aschmidt99/LTDM_Kit_RevC/Electronics/spice_simulations/Draft1.asc

R1: res; {R}
R2: res; {R}
R3: res; {R}
R4: res; {R}
U1: UniversalOpAmp2; Avol=100K GBW=300Meg Slew=140Meg
V1: voltage; PULSE(0 3.3 0 5n 5n 15u 50u 10)
V2: voltage; 12
V3: voltage; 12
Named nets: 0, -12V, +12V
.tran .00002
.step param R list 100 1k 10k
