aschmidt99/LTDM_Kit_RevC/Electronics/spice_simulations/Input_Stage.asc

A1: sample
B1: bv; V=V(act) + V(vib) + V(actback)
C1: cap; 60p
C2: cap; 60p
C3: cap; 0
R1: res; 2.2
R2: res; 0
R3: res; 1k
R4: res; 100
R5: res; 100
R6: res; 1k
R7: res; 3.1k
R8: res; .5
R9: res; 31k
R10: res; 100
R11: res; 1.47k
R12: res; 100
R13: res; 1k
R14: res; 1k
R15: res; 100
R16: res; 1.47k
R17: res; 100
R18: res; 1k
U1: UniversalOpAmp2
U2: UniversalOpAmp2
U3: UniversalOpAmp2
U4: UniversalOpAmp2
V1: voltage; SINE(0 1m 1000 0 0 0 50)
V2: voltage; 12
V3: voltage; 12
V4: voltage; SINE(0 10m 500 0 0 0 50)
V5: voltage; SINE(0 -1m 1000 0 0 0 50)
V6: voltage; SINE(0 0 100 0 0 0 50)
V7: voltage; PULSE(0 12 10u 1n 1n 25u 50u 1000)
V8: voltage; PULSE(0 5 2u 1n 1n 15u 50u 1000)
V9: voltage; PULSE(0 -12 35u 1n 1n 2u 50u 1000)
Named nets: 0, +12, -12, act, vib, actback
.tran 0.0001
*.step param R list 470 1k 10k
