aschmidt99/LTDM_Kit_RevC/Electronics/spice_simulations/LF-TIME-MULTIPLEX-ACTUATION+SENSE.asc

10k: res; 1k
11: res; 11
A1: sample
A2: sample
A3: xor
A4: and
A5: and
B1: bv; V= V(vib) + V(STRING_IN)
B2: bv; V= IF(V(ramp) < V(vib), 3.3V, 0)
B3: bv; V= IF(V(ramp) < -V(vib), 3.3V, 0)
B4: bv; V= V(vib)*496
B5: bv; V{if(V(over_current)>100mV, 3.3V, 0)}
B6`: bi; I=1-V(over_current_flag)
C1: cap; 100p
C2: cap; 60p
C3: cap; 60p
C4: cap; 0
C5: cap; 220p
C6: cap; 220p
C7: cap; 220p
C8: cap; 10n
C9: cap; 10n
C10: cap; 20n
C11: cap; 10n
C12: cap; 4.7n
C13: cap; 1000µ
C14: cap; 220µ
C15: cap; 10µ
C16: cap; 100n
D1: TVSdiode
I1: current; 10m
L1: ind; .47µ
L2: ind; .05µ
L3: ind; 0.05µ
M1: pmos; FQB11P06
M2: nmos
M3: nmos; BSC205N10LS
Q1: npn; 2N3904
Q3: pnp; 2N3906
R1: res; 220
R2: res; 470
R3: res; 2
R4: res; 220
R5: res; 100
R6: res; 470
R7: res; 1k
R8: res; .1
R9: res; 100
R10: res; 1k
R11: res; 3.1k
R12: res; 31k
R13: res; 100
R14: res; 1.47k
R15: res; 100
R16: res; .5
R17: res; 1k
R18: res; 1k
R19: res; 100
R20: res; 1.47k
R21: res; 100
R22: res; 11
R23: res; 1k
R24: res; 1k
R25: res; 1k
R26: res; 1k
R27: res; 1k
R28: res; 221
R29: res; 1k
R30: res; 100
R31: res; 0.05
R32: res; 221
R33: res; 1k
R34: res; 100
R35: res; .5
R36: res; 800
R37: res; 800
R38: res; 1k
R39: res; 10k
R40: res; 400
R41: res; 2.2k
R42: res; 2.2k
R43: res; 220
R44: res; 1k
R45: res; 1k
R46: res; 1k
R47: res; 1k
R48: res; 1k
R49: res; 10k
U1: UniversalOpAmp2
U2: UniversalOpAmp2
U3: UniversalOpAmp2
U4: UniversalOpAmp2
U5: UniversalOpAmp2
U6: UniversalOpAmp2
U7: UniversalOpAmp2
U8: UniversalOpAmp2
U9: UniversalOpAmp2
U10: UniversalOpAmp
U11: UniversalOpAmp
U12: UniversalOpAmp
V1: voltage; PULSE(0 5 0 1n 1n 15u 50u 2000)
V2: voltage; 12
V3: voltage; 12
V4: voltage; 3.3
V5: voltage; SINE(0 11m 1k 0 0 0 500); AC 1
V6: voltage; 3.3V
V7: voltage; PULSE(0 1 0 1 0 0 500); AC 1
V8: voltage; PULSE(0 5 2u 1n 1n 15u 50u 1000)
V10: voltage; PULSE(0 12m 10u 30u 0.5n 20u 50u 20000)
Named nets: VEE, 0, VCC, VCC_PRIME, STRING_IN, Current_Sense, vib, ramp, P_PULSE, N_PULSE, SH_preamp_out, preamp_out, SH_out, SUM, SH_preamp_out_2, preamp_out_2, SH_out_2, Pre_SH2, post, S+H, vib_500, LP, TwinT, VCC_prime, 3V3, over_current, over_current_flag
*.tran 0 750u 650u
E = 1 "Left"
B = 2 = "Center"
C = 3 = "RIGHT"
E = 1 "Left"
B = 2 = "Center"
C = 3 = "RIGHT"
G = 1 "Left"
D = 2 "Center"
S = 3 "RIGHT"
G = 1 "Left"
S = 3 "RIGHT"
D = 2 "Center"
Simulation of Lorentz-Force Actuation via time-multiplexing
Found Negative supply solution here: https://forum.allaboutcircuits.com/threads/simplest-way-to-switch-a-negative-voltage-using-logic-level-signals.172313/
Found Positive supply solution here: https://forum.arduino.cc/t/3-3v-logic-to-drive-p-channel-mosfet/685383
RAMP SIGNAL
P_PULSE
P_PULSE
Voltage induced by vibration of string
.tran 2
.lib OPA161x.LIB
Current Limiting Resistor
String Resistance
*.ac dec 1K 10 100K
*.tran 2
XOR to prevent shoot through
