aschmidt99/LTDM_Kit_RevC/Electronics/spice_simulations/LF-TIME-MULTIPLEX-ACTUATION.asc

10k: res; 1k
C1: cap; 100p
D1: schottky; 1N5817
D3: diode
L1: ind; .1µ
L2: ind; .01µ
M1: pmos; FQB11P06
M3: nmos; BSC205N10LS
Q1: npn; 2N3904
Q3: pnp; 2N3906
R1: res; 220
R2: res; 470
R3: res; 1
R4: res; 220
R5: res; 200
R6: res; 470
R7: res; 1k
R8: res; .1
V1: voltage; PULSE(0 3.3 0 .5n 0.5n 15u 100u 20)
V2: voltage; 12
V3: voltage; 12
V4: voltage; PULSE(0 3.3 50u 1n 1n 15u 100u 20)
Named nets: 0, VEE, VCC, STRING_IN, R_sense
.tran 1000u
E = 1 "Left"
B = 2 = "Center"
C = 3 = "RIGHT"
E = 1 "Left"
B = 2 = "Center"
C = 3 = "RIGHT"
G = 1 "Left"
D = 2 "Center"
S = 3 "RIGHT"
G = 1 "Left"
S = 3 "RIGHT"
D = 2 "Center"
Simulation of Lorentz-Force Actuation via time-multiplexing
Found Negative supply solution here: https://forum.allaboutcircuits.com/threads/simplest-way-to-switch-a-negative-voltage-using-logic-level-signals.172313/
Found Positive supply solution here: https://forum.arduino.cc/t/3-3v-logic-to-drive-p-channel-mosfet/685383
