aschmidt99/LTDM_Kit_RevC/Electronics/spice_simulations/Sallen-Key.asc

C2: cap; 10n
C3: cap; 4.7n
R1: res; 2.2k
R2: res; 2.2k
U2: UniversalOpAmp2
V1: voltage; ""; AC 1
V2: voltage; 12
V3: voltage; 12
Named nets: VCC, VEE, 0, in, out
.ac dec 1K 10 20K
