aschmidt99/LTDM_Kit_RevC/Code/LTDM_Kit/LTDM_Kit.ino

/* This code creates precisely timed pulses for sustaining vibrations of a resonant system, like Figure 2 of Paul Vo's Patent: [https://patents.google.com/patent/EP1218716B1](https://patents.google.com/patent/EP1218716B1)

For Teensy 4.1 with RevB or RevC PCB plugged into the UI PCB OR controlled over serial
*/

#include "imxrt.h"
#include "core_pins.h"
#include "debug/printf.h"
#include <Arduino.h>
#include <SPI.h>
#include "SineTable.h"
#include "Adafruit_TLC5947.h"

#include "pinmap.h"
#include "debug.h"
#include "flexpwm.h"
#include "ui.h"
#include "system_config.h"
#include "harmonics.h"
#include "context.h"
#include "render.h"
#include "serialctrl.h"
#include "capture_stream.h"

void setup() {
  delay(2000);               // Wait for 2 seconds before starting the setup
  Serial.begin(2000000);     // Initialize serial communication at 2,000,000 baud rate
  analogReadResolution(12);  // default should be 12
  analogReadAveraging(0);    // Disable averaging (set to 0) for faster reading... 3 seems to be fine, but 4 is far too much
  initUI();                  // initialize the UI (declare pins etc.)
  initFlexPWM();             // initialize FlexPWM
  pinMode(GPIO_PIN, OUTPUT); // set GPIO_PIN as output
  renderSetup(&context);     // setup rendering context
  setInterrupts();           // enable interrupts
  initSineTable();           // initialize sine table
  captureStreamSetup();      // initialize capture stream
}

void loop() {
  captureStreamLoop();       // handle capture stream loop
  pollSerialControl();       // handle serial control polling
  output();                  // update UI and output states
}
