aschmidt99/LTDM_Kit_RevC/Code/LTDM_Kit/debug.h

// debug.h
#ifndef DEBUG_H
#define DEBUG_H

#ifdef DEBUG
  #define DEBUG_PRINT(x)    Serial.print(x)
  #define DEBUG_PRINTLN(x)  Serial.println(x)
#else
  #define DEBUG_PRINT(x)
  #define DEBUG_PRINTLN(x)
#endif

#endif
