aschmidt99/LTDM_Kit_RevC/Code/LTDM_Kit/context.h

// context.h
#ifndef CONTEXT_H
#define CONTEXT_H

#include "system_config.h"
#include "channel.h"

struct LorentzContext {
    // INPUTS - populated by the ISR before render() is called
    Channel ch[2];

    // Hardware inputs
    bool  buttons[16];       // all button states
    float sliders[16];       // all slider/pot values, normalised 0.0-1.0
    float pedals[2];     // both expression pedal values
    uint32_t isrCycleCount;
    uint32_t renderCycleCount;
    unsigned long long frameCount; // total samples elapsed, useful for LFOs etc.
};

extern LorentzContext context;

#endif
