aschmidt99/LTDM_Kit_RevC/Code/LTDM_Kit/ui.cpp

// ui.cpp
#include "ui.h"
#include "pinmap.h"
#include "flexpwm.h"
#include <Arduino.h>
#include <SPI.h>
#include "Adafruit_TLC5947.h"
#include <cstdint>
#include "render.h"
#include "serialctrl.h"
#include "capture_stream.h"

extern float currRMS0;
extern float currRMS1;

volatile bool buttonStates[16] = {};
volatile float sliderStates[16] = {};
volatile float pedalStates[2] = {};

uint8_t currentInput = 0;
bool UI_ReadPhase = false;
uint32_t lastPrint = 0;

float invNumCyclesPerSample = 1.0f;

extern Adafruit_TLC5947 tlc = Adafruit_TLC5947(1, tlc_clock, tlc_data, tlc_latch);

void initUI() {
  pinMode(DSIN, INPUT_PULLUP);
  pinMode(DS0, OUTPUT);
  pinMode(DS1, OUTPUT);
  pinMode(DS2, OUTPUT);
  pinMode(DS3, OUTPUT);

  pinMode(ASIN, INPUT);
  pinMode(AS0, OUTPUT);
  pinMode(AS1, OUTPUT);
  pinMode(AS2, OUTPUT);
  pinMode(AS3, OUTPUT);

  pinMode(FP0, INPUT);
  pinMode(FP1, INPUT);

  digitalWrite(DS0, LOW);
  digitalWrite(DS1, LOW);
  digitalWrite(DS2, LOW);
  digitalWrite(DS3, LOW);
  
  digitalWrite(AS0, LOW);
  digitalWrite(AS1, LOW);
  digitalWrite(AS2, LOW);
  digitalWrite(AS3, LOW);

  tlc.begin();
}

// void initServo(){
//   servo.attach(SERVO_PIN);
// }

// Remap table: reorders where each pot value is stored (since the default hardware inputs was wack)
const uint8_t sliderRemap[16] = {7, 6, 5, 4, 0, 1, 2, 3, 8, 9, 10, 11, 12, 13, 14, 15};

void readUI(){
  if (!UI_ReadPhase) {
    // MUX select pins based on currentButton index
    digitalWrite(DS0, currentInput & 0x01);
    digitalWrite(DS1, (currentInput >> 1) & 0x01);
    digitalWrite(DS2, (currentInput >> 2) & 0x01);
    digitalWrite(DS3, (currentInput >> 3) & 0x01);
    digitalWrite(AS0, currentInput & 0x01);
    digitalWrite(AS1, (currentInput >> 1) & 0x01);
    digitalWrite(AS2, (currentInput >> 2) & 0x01);
    digitalWrite(AS3, (currentInput >> 3) & 0x01);
    UI_ReadPhase = 1;
  } else {
    if (!serialOverride) {
      buttonStates[currentInput] = (digitalRead(DSIN) == LOW);
      sliderStates[sliderRemap[currentInput]] = float(analogRead(ASIN)/4096.);
      if (currentInput == 0) {pedalStates[0] = float(analogRead(FP0)/4096.);}
      else if (currentInput == 1) {pedalStates[1] = float(analogRead(FP1)/4096.);}
    }
    // Move to next button
    currentInput = (currentInput + 1) & 0x0F;
    UI_ReadPhase = 0;
  }
}

void updateLEDsFromButtons() {
  //tlc.setLED(LED_INDEX, R, G, B);
  // CH1
  tlc.setLED(0, 0, 500*sliderStates[0]*buttonStates[0], 0); // LED one is green, scaled by feedback gain

  tlc.setLED(2, 500*!buttonStates[2]*buttonStates[0], 0, 500*context.ch[0].targetRMS*buttonStates[0]*(buttonStates[2])); // BLUE intensitiy represents target RMS - Red indicated RMS limiting is off

  tlc.setLED(4, 500*context.ch[0].measuredRMS, 250*context.ch[0].measuredRMS, 0); // Current RMS indicator

  tlc.setLED(6, 500*sliderStates[3]*buttonStates[6]*buttonStates[0], 500*sliderStates[3]*buttonStates[6]*(sliderStates[2])*buttonStates[0], 500*sliderStates[3]*buttonStates[6]*buttonStates[0]); // turn LED on when noise is active. Scale from white to pink

  // CH2
  tlc.setLED(1, 0, 500*sliderStates[4]*buttonStates[1], 0); // CH2 - turn LED on when active

  tlc.setLED(3, 500*!buttonStates[3]*buttonStates[1], 0, 500*context.ch[1].targetRMS*buttonStates[1]*(buttonStates[3])); // BLUE intensitiy represents target RMS - Red indicated RMS limiting is off

  tlc.setLED(5, 500*context.ch[1].measuredRMS, 250*context.ch[1].measuredRMS, 0); // Current RMS indicator

  tlc.setLED(7, 500*sliderStates[7]*buttonStates[7]*buttonStates[1], 500*sliderStates[7]*buttonStates[7]*(sliderStates[6])*buttonStates[1], 500*sliderStates[7]*buttonStates[7]*buttonStates[1]); // turn LED on when noise is active. Scale from white to pink
  
  tlc.write();
  delay(1);
}

// void updateServo(){
//   servo.write(sliderStates[8]*180*buttonStates[8]);
// }

// this is naughty ... I have tied together serial printing and updating the buttons
void output() {
  // put your main code here, to run repeatedly:
  if (captureStreamIsArmed() || captureStreamIsActive()) {
    updateLEDsFromButtons();
    // updateServo();
    return;
  }

  if (millis() - lastPrint > 100) { // update every 100 ms

    invNumCyclesPerSample = (float)SAMPLERATE / (float)F_BUS_ACTUAL;
    lastPrint = millis();
    for (int i = 0; i < 16; i++){
      Serial.print(buttonStates[i]);
    }
    for (int i = 0; i < 16; i++){
      Serial.print(" ");
      Serial.print(sliderStates[i]);
    }
    Serial.print(" ");
    Serial.print(pedalStates[0]);
    Serial.print(" ");
    Serial.print(pedalStates[1]);

    Serial.println();
    Serial.print("adcScale: ");
    Serial.print(context.ch[0].adcScale);
    Serial.print(" targetRMS: ");
    Serial.print(context.ch[0].targetRMS);
    Serial.print(" measuredRMS: ");
    Serial.print(context.ch[0].measuredRMS);
    Serial.print(" noiseScale: ");
    Serial.print(" ");
    Serial.print(context.ch[0].noiseScale);
    Serial.println();

    Serial.print("adcScale: ");
    Serial.print(context.ch[1].adcScale);
    Serial.print(" targetRMS: ");
    Serial.print(context.ch[1].targetRMS);
    Serial.print(" measuredRMS: ");
    Serial.print(context.ch[1].measuredRMS);
    Serial.print(" noiseScale: ");
    Serial.print(" ");
    Serial.print(context.ch[1].noiseScale);
    Serial.println();

    Serial.print(currRMS0);
    Serial.println();

    Serial.print(" Render cycle Count: ");
    Serial.print(" ");
      Serial.print(context.renderCycleCount);
    Serial.println();

    Serial.print("Render cpu load: ");
    Serial.print(" ");
    Serial.print(context.renderCycleCount * invNumCyclesPerSample);
    Serial.println();
    updateLEDsFromButtons();
    // updateServo();

        Serial.print(" ISR cycle Count: ");
    Serial.print(" ");
      Serial.print(context.isrCycleCount);
    Serial.println();

    Serial.print(" ISR cpu load: ");
    Serial.print(" ");
    Serial.print(context.isrCycleCount * invNumCyclesPerSample);
    Serial.println();
    updateLEDsFromButtons();
    // updateServo();
  }
}
