aschmidt99/LTDM_Kit_RevC/Code/LTDM_Kit/ui.h

// ui.h
#ifndef UI_H
#define UI_H

#include <Arduino.h>
#include "Adafruit_TLC5947.h"

extern uint8_t currentInput;
extern bool UI_ReadPhase;
extern uint32_t lastPrint;
extern Adafruit_TLC5947 tlc;

// Button state array
extern volatile bool buttonStates[16];
extern volatile float sliderStates[16];
extern volatile float pedalStates[2];

void initUI();
void readUI();
void updateLEDsFromButtons();
void output();

#endif
